mpfisher69/R2R-Bluetooth-Remote/Images/btr_app02.jpg

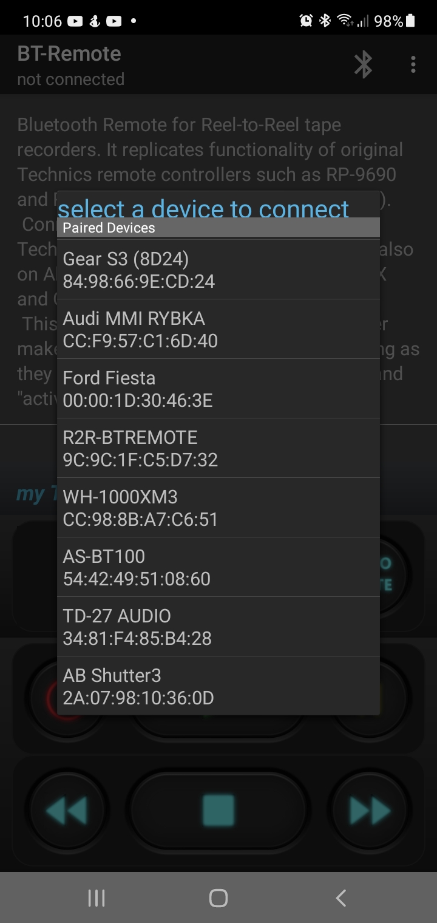
Images/btr_app02.jpg
